mibbbbbn7/ergo_mibbbbbn/Pics/Fusion360/pi_pico_seat.png

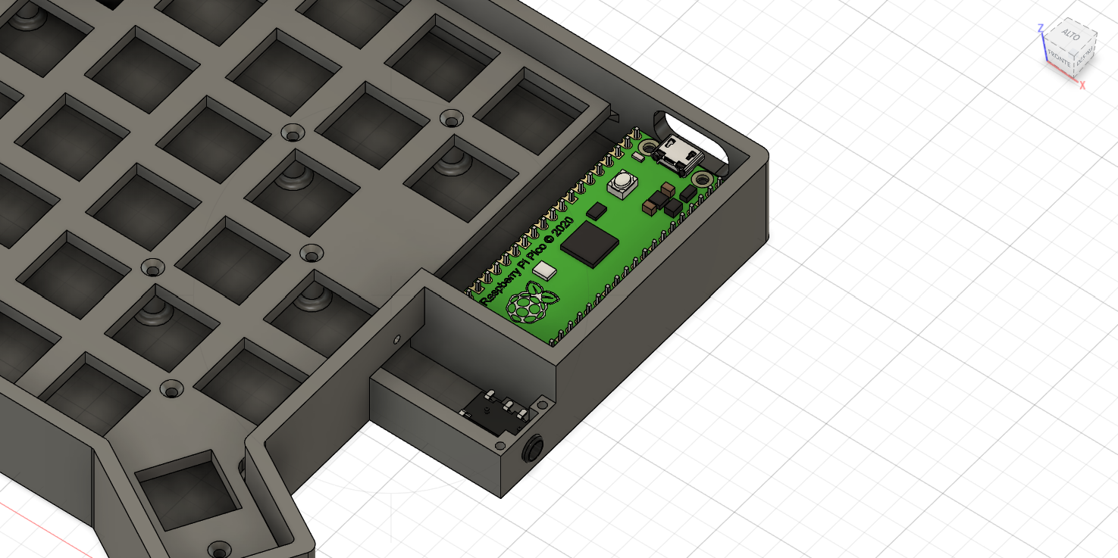
Pics/Fusion360/pi_pico_seat.png
