mibbbbbn7/ergo_mibbbbbn/Pics/Fusion360/top_view.png

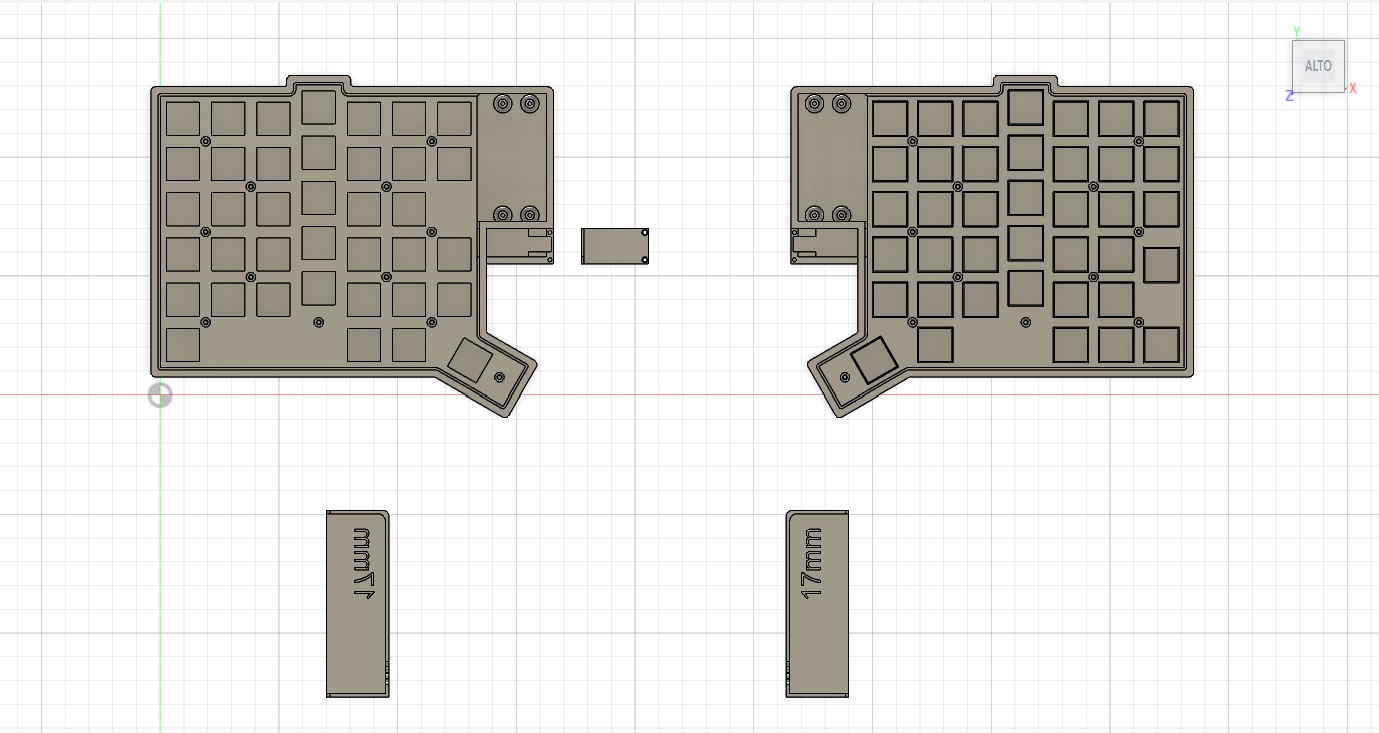
Pics/Fusion360/top_view.png
