mibbbbbn7/ergo_mibbbbbn/Pics/Photos/flat_2.jpg

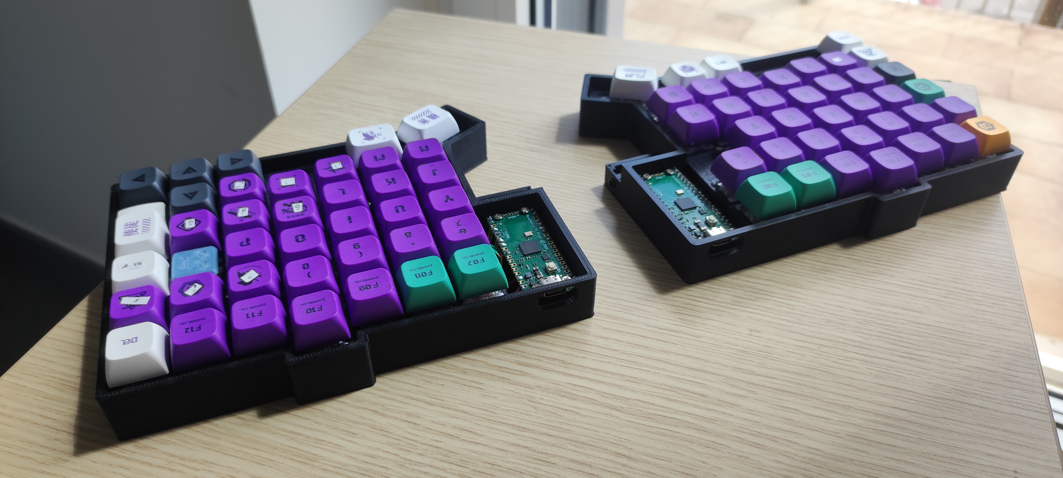
Pics/Photos/flat_2.jpg
