mibbbbbn7/ergo_mibbbbbn/Pics/Photos/initialize_button_1.jpg

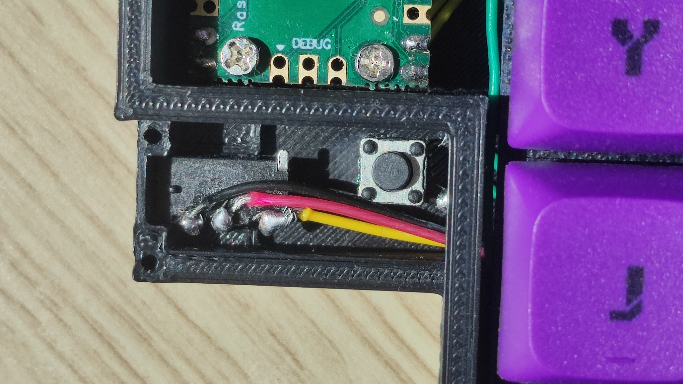
Pics/Photos/initialize_button_1.jpg
