mibbbbbn7/ergo_mibbbbbn/Pics/Photos/rise_trs_1.jpg

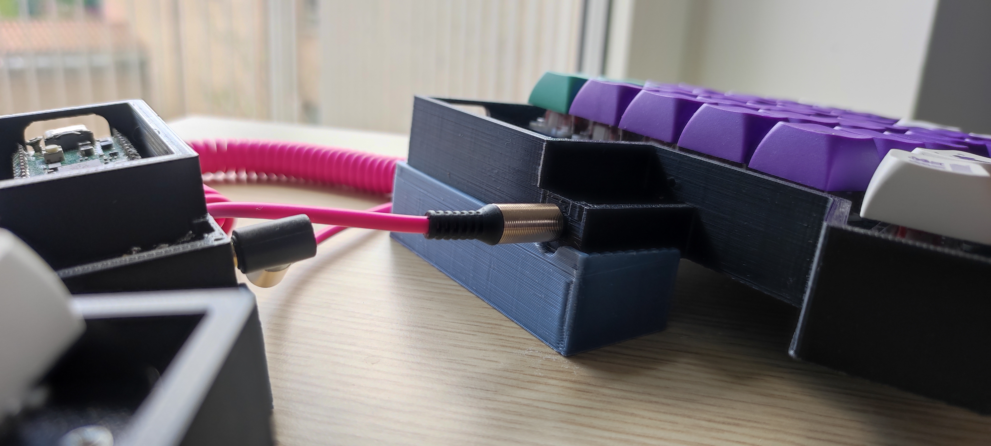
Pics/Photos/rise_trs_1.jpg
