mibbbbbn7/ergo_mibbbbbn/Pics/Photos/wiring_1.jpg

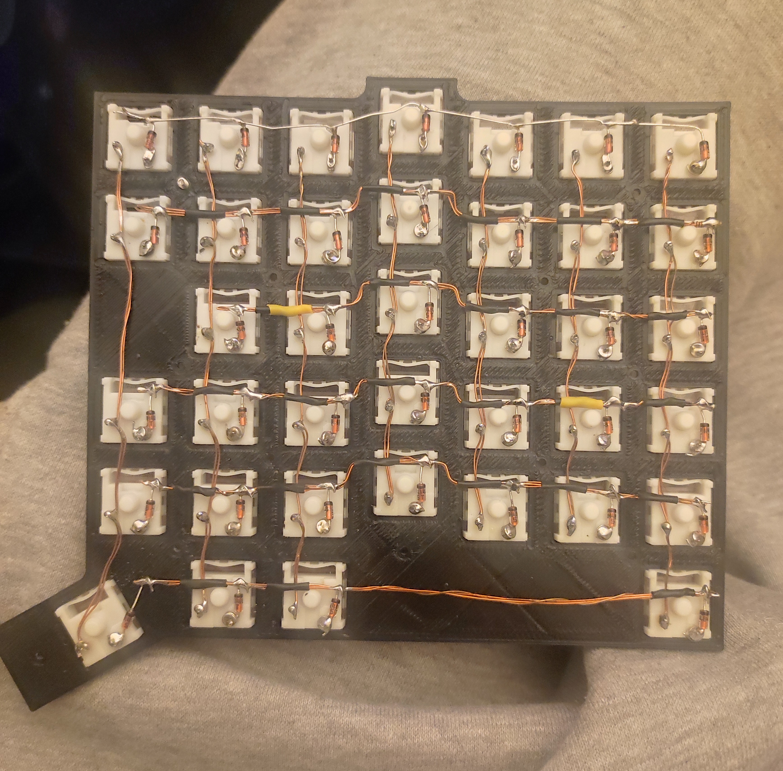
Pics/Photos/wiring_1.jpg
