mibbbbbn7/ergo_mibbbbbn/Pics/Photos/wiring_pretty_2.jpg

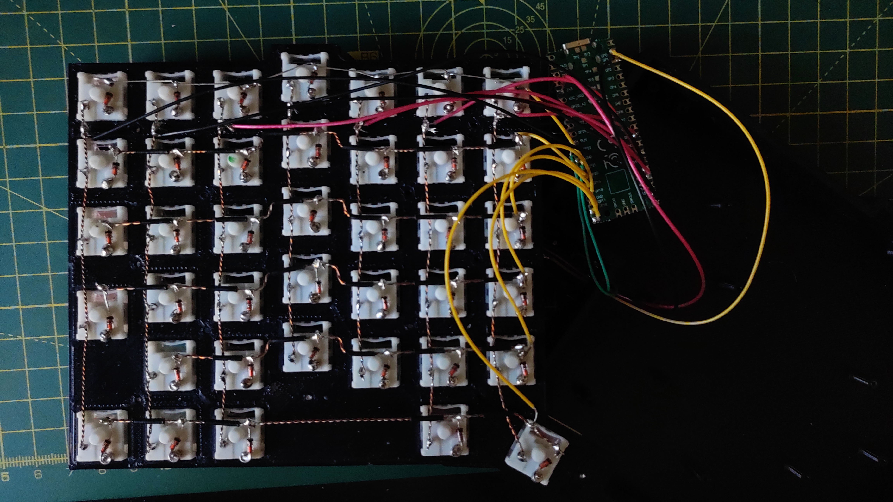
Pics/Photos/wiring_pretty_2.jpg
