mibbbbbn7/ergo_mibbbbbn/Wiring/left_wireing.png

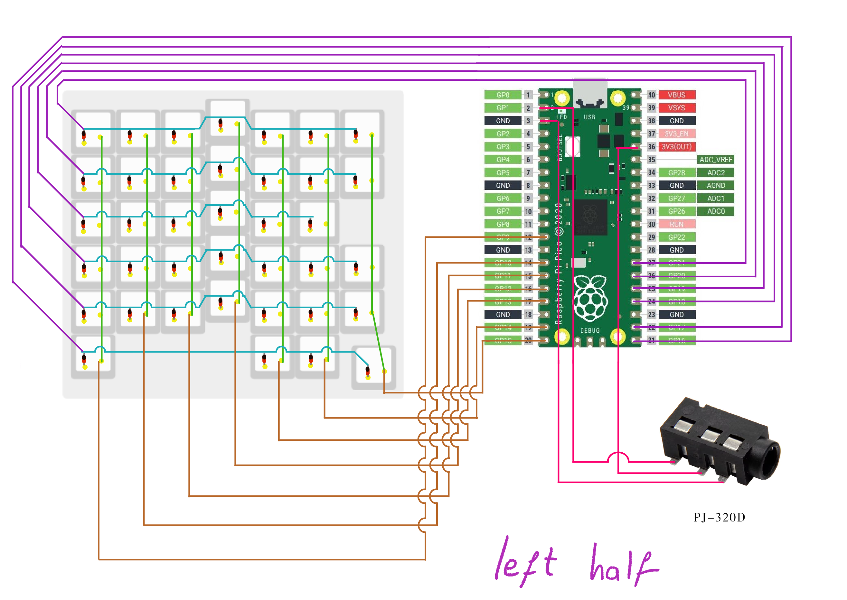
Wiring/left_wireing.png
