mibbbbbn7/ergo_mibbbbbn/Wiring/left_wiring_pic.jpg

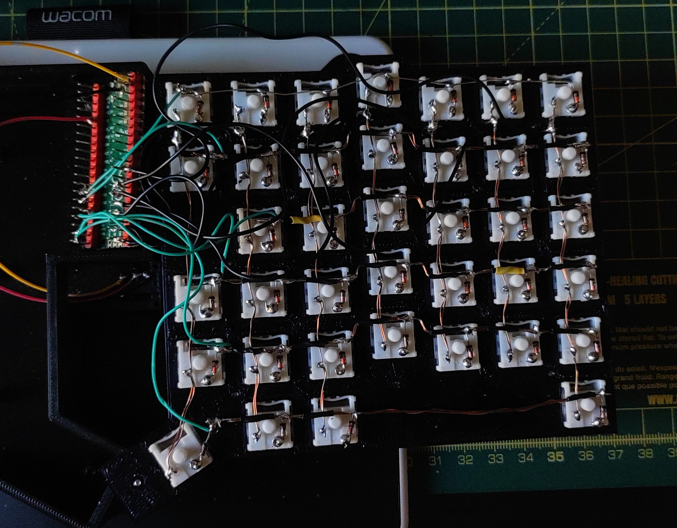
Wiring/left_wiring_pic.jpg
