mibbbbbn7/ergo_mibbbbbn/Wiring/right_wiring.png

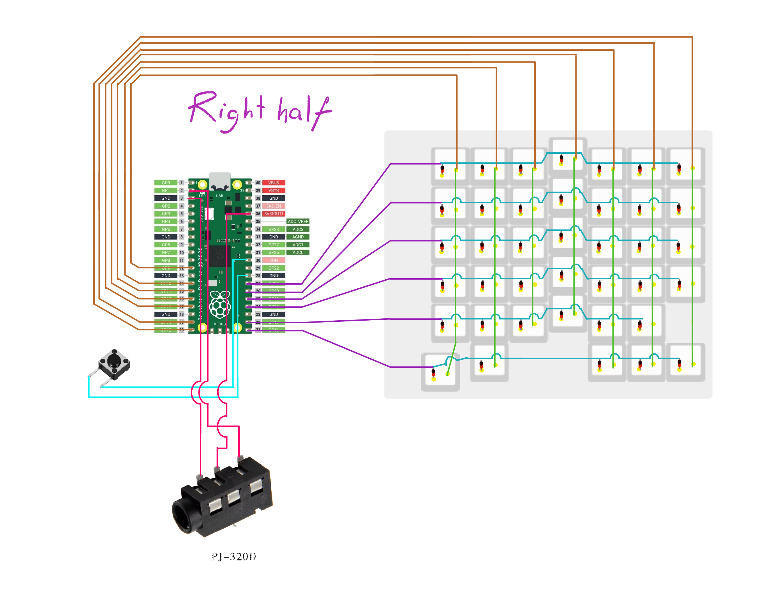
Wiring/right_wiring.png
